hazeeqazfar01/Roboter_Design_Challenge/Pictures/1.jpeg

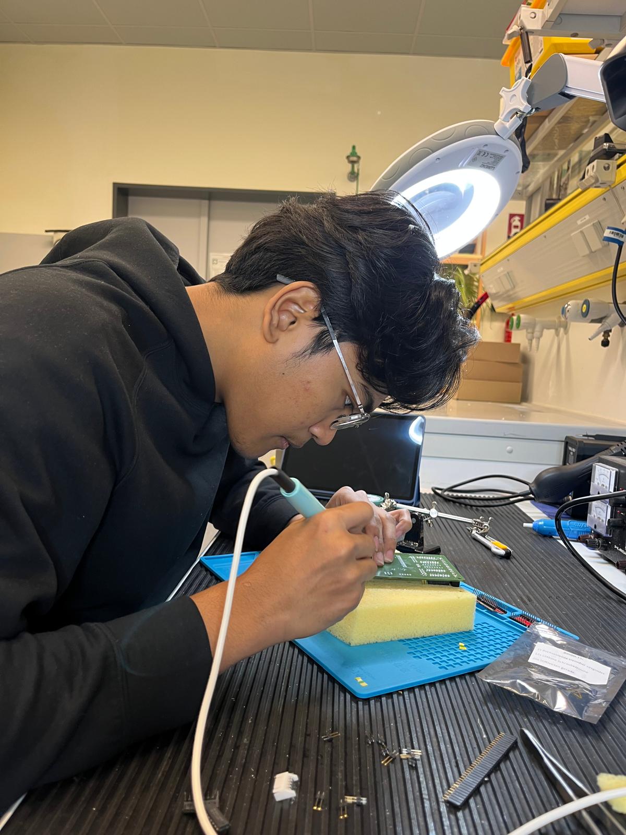
Pictures/1.jpeg
