hazeeqazfar01/Roboter_Design_Challenge/Pictures/2WhatsApp Image 2026-04-02 at 15.36.26.jpeg

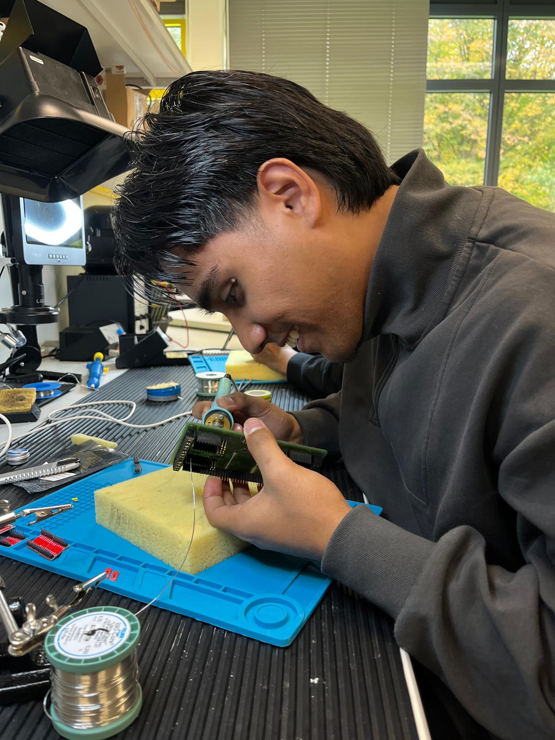
Pictures/2WhatsApp Image 2026-04-02 at 15.36.26.jpeg
