hazeeqazfar01/Roboter_Design_Challenge/Pictures/3.jpeg

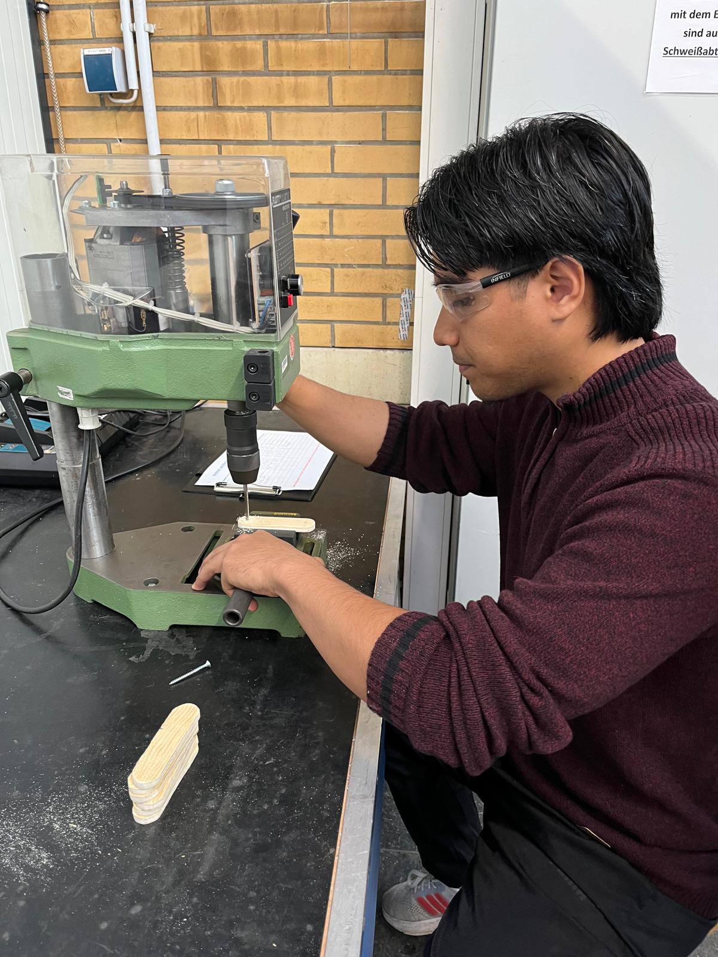
Pictures/3.jpeg
