hazeeqazfar01/Roboter_Design_Challenge/Pictures/4.jpeg

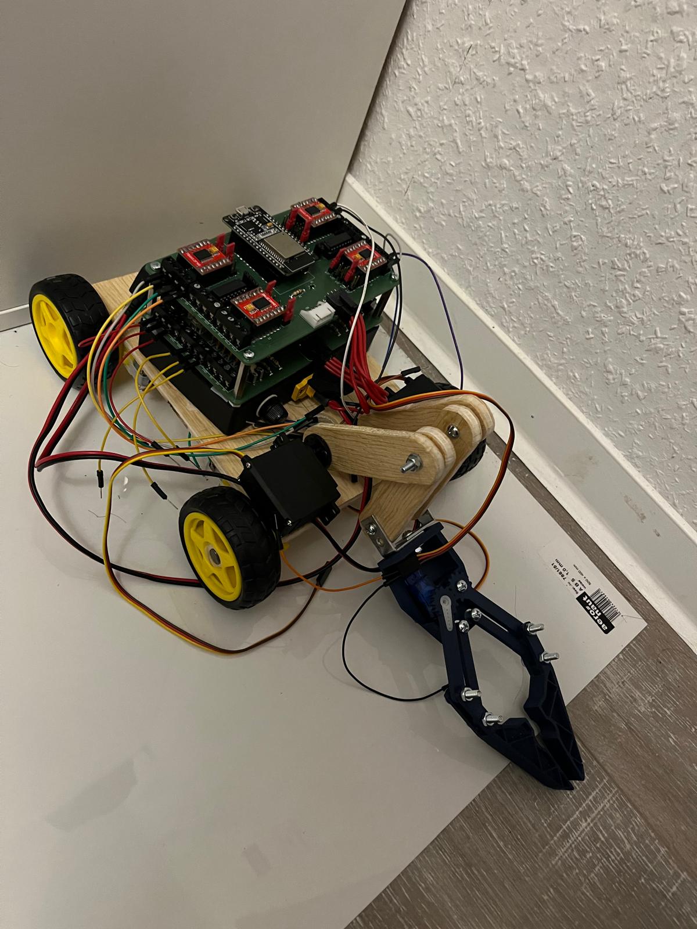
Pictures/4.jpeg
