hazeeqazfar01/Roboter_Design_Challenge/Pictures/5.jpeg

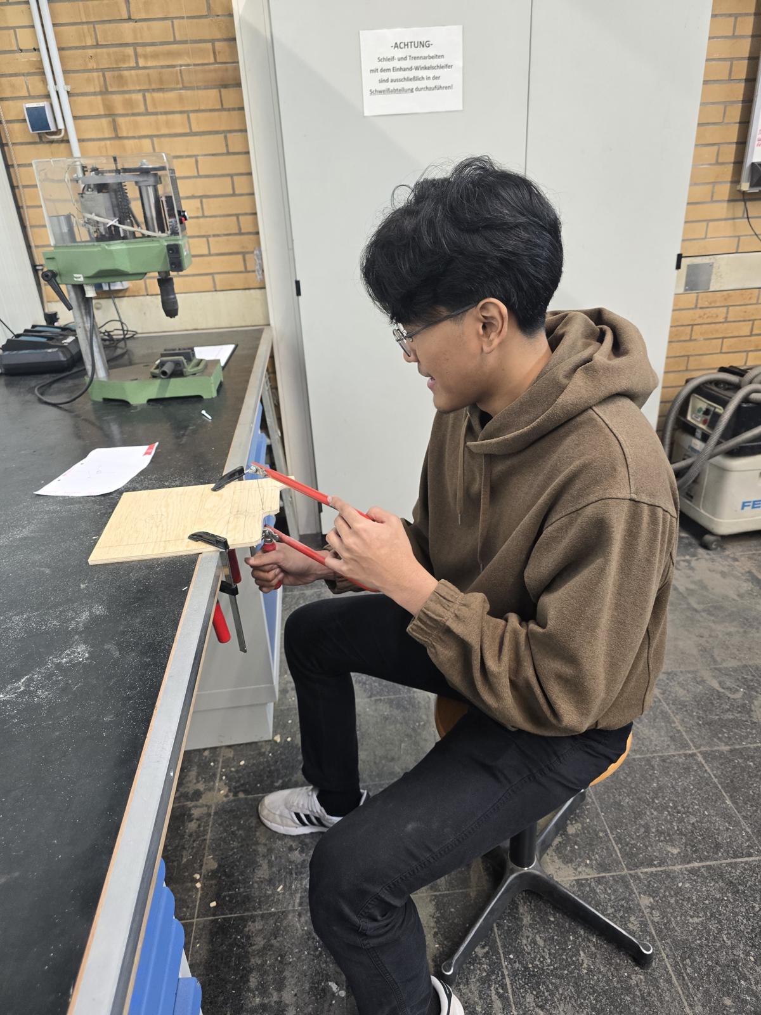
Pictures/5.jpeg
