hazeeqazfar01/Roboter_Design_Challenge/Pictures/7.jpeg

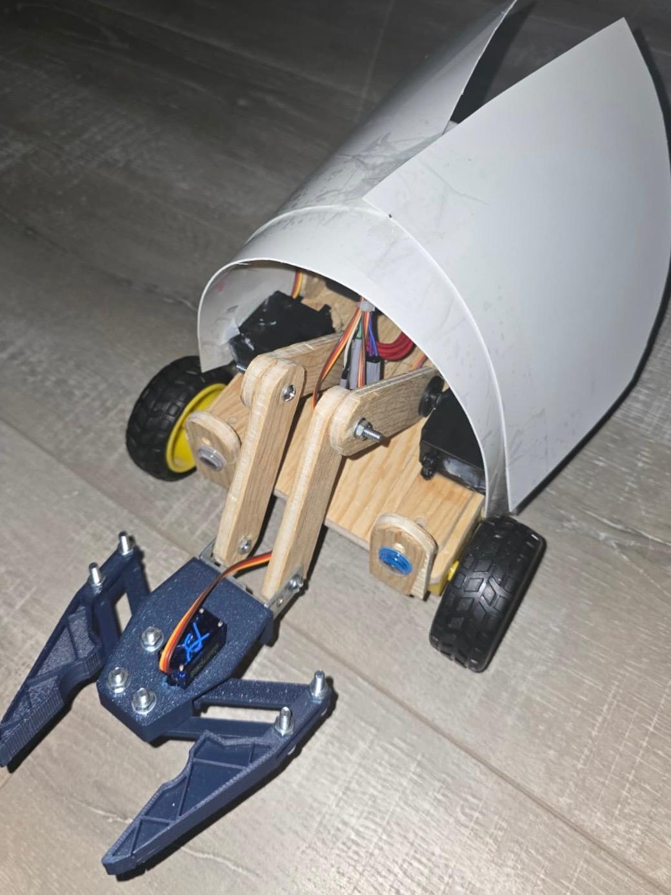
Pictures/7.jpeg
