hazeeqazfar01/Roboter_Design_Challenge/Pictures/8.jpeg

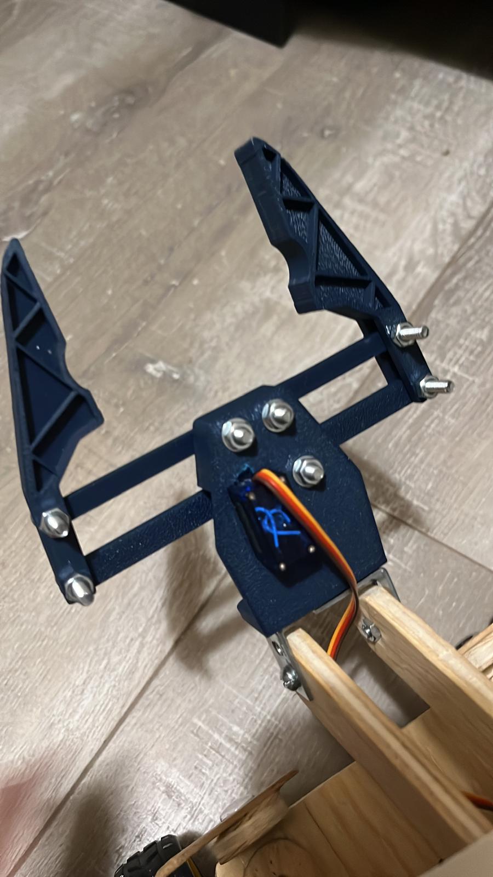
Pictures/8.jpeg
