hazeeqazfar01/Roboter_Design_Challenge/Pictures/9.jpeg

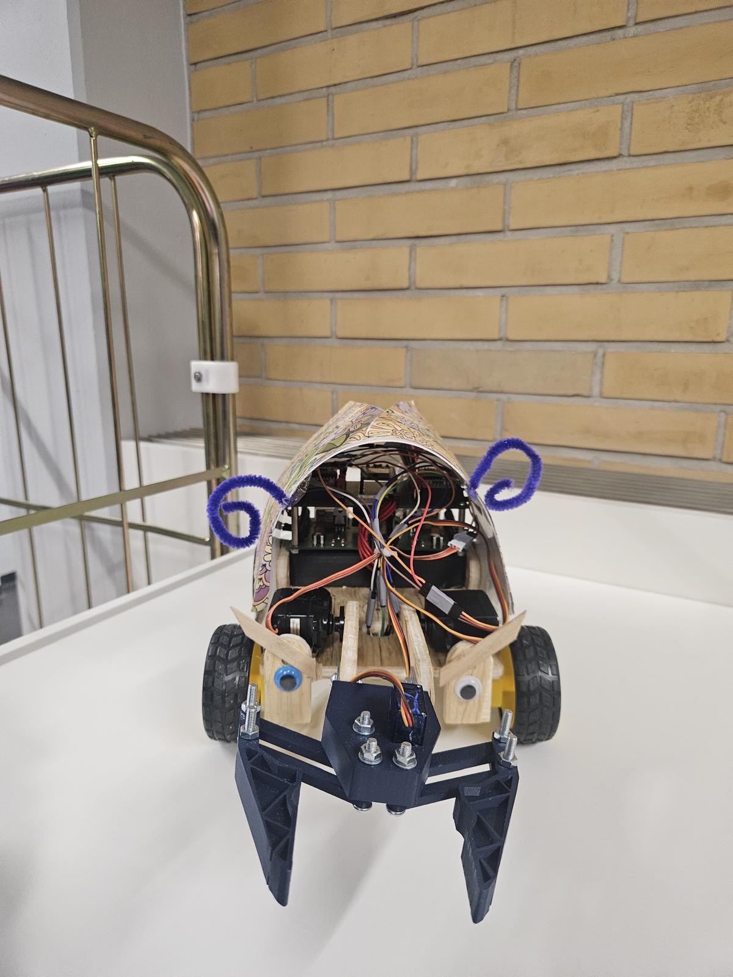
Pictures/9.jpeg
