hazeeqazfar01/Roboter_Design_Challenge/Pictures/45.jpeg

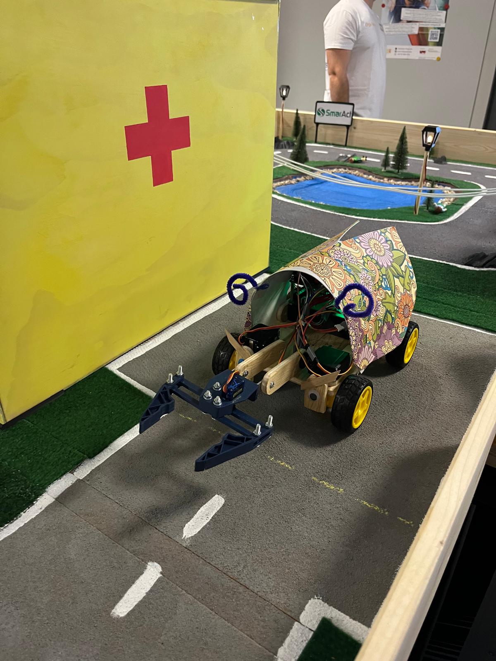
Pictures/45.jpeg
