hazeeqazfar01/Roboter_Design_Challenge/Pictures/334.jpeg

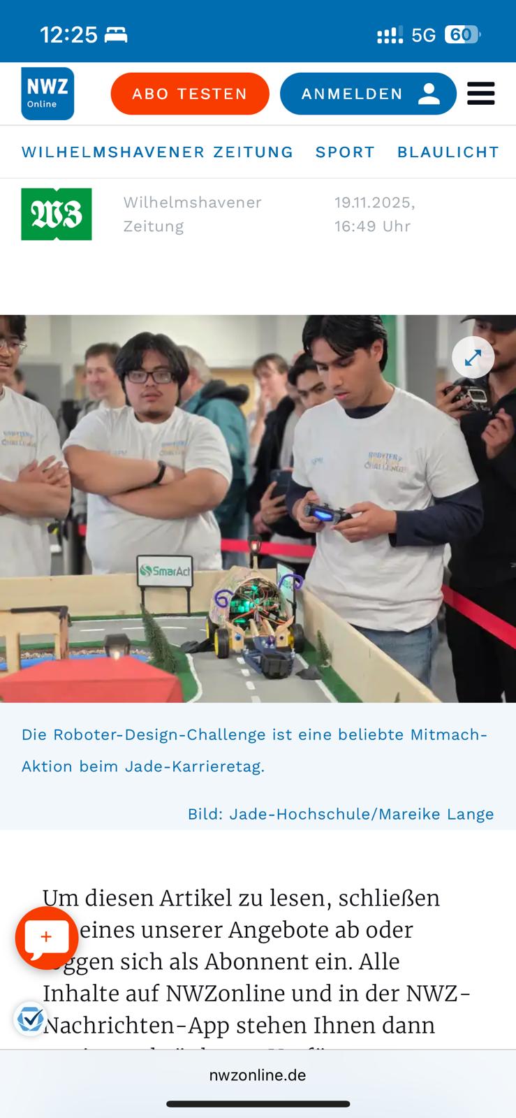
Pictures/334.jpeg
