hazeeqazfar01/Roboter_Design_Challenge/Pictures/3428.jpeg

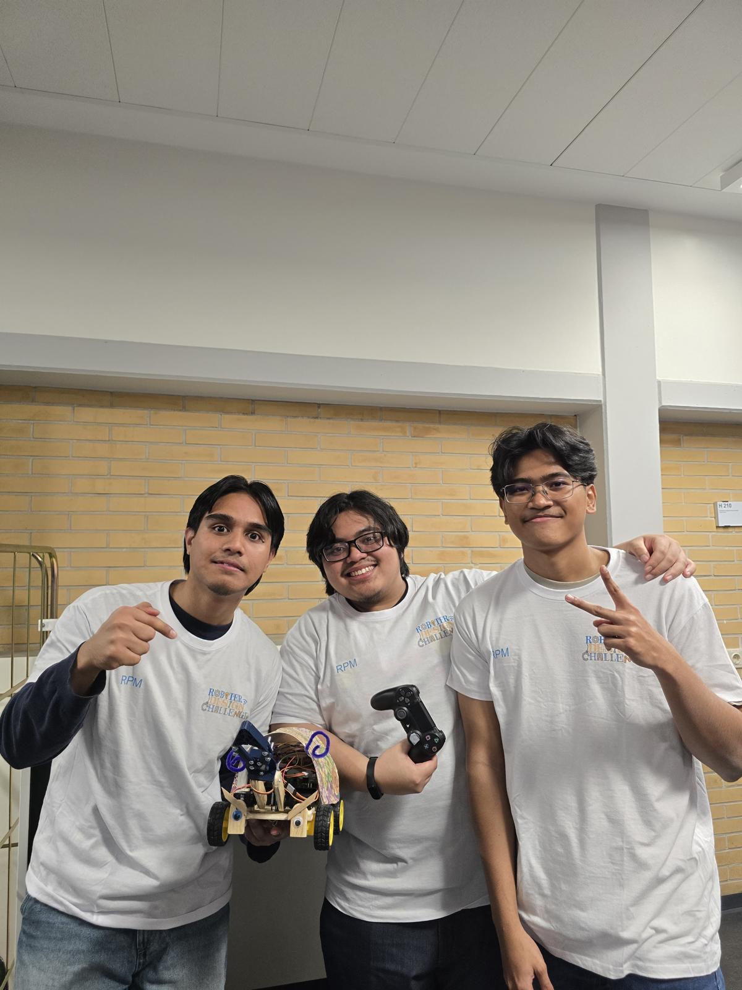
Pictures/3428.jpeg
