hazeeqazfar01/Roboter_Design_Challenge/Pictures/WhatsApp Image 2025-11-19 at 3.07.54 PM.jpeg

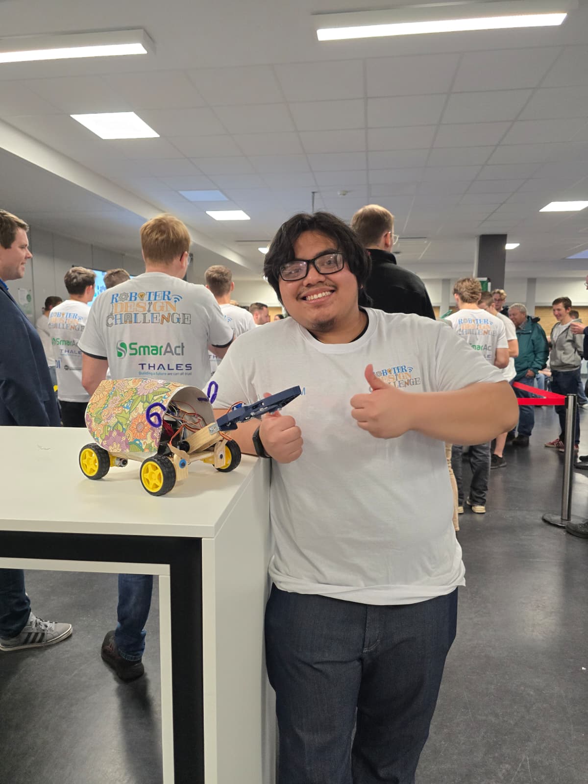
Pictures/WhatsApp Image 2025-11-19 at 3.07.54 PM.jpeg
