hazeeqazfar01/Roboter_Design_Challenge/Pictures/WhatsApp Image 2026-03-29 at 21.02.25.jpeg

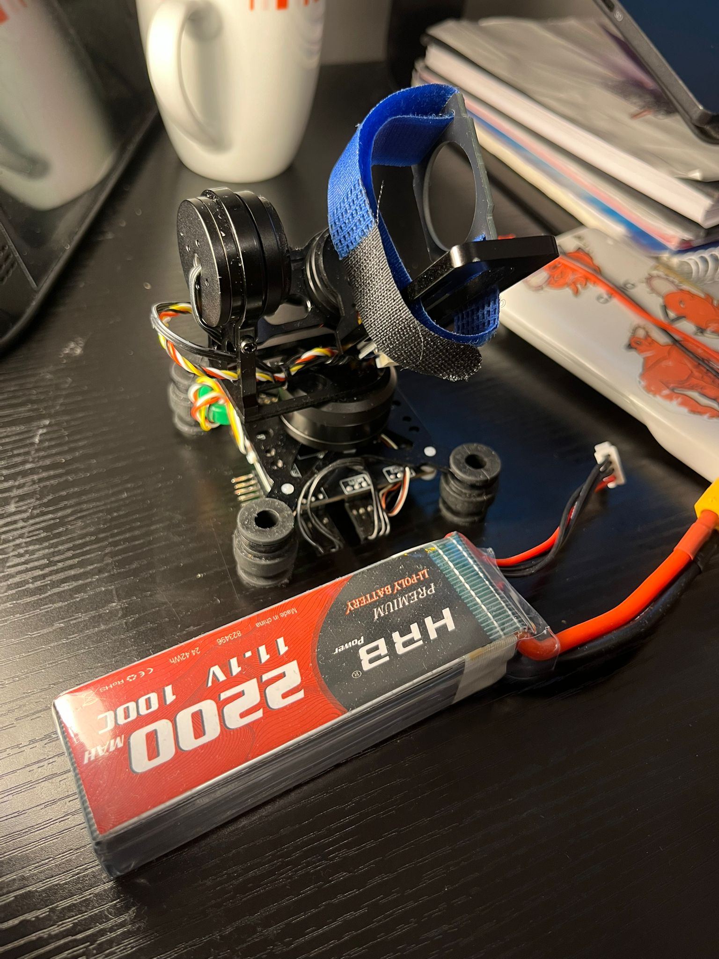
Pictures/WhatsApp Image 2026-03-29 at 21.02.25.jpeg
