hazeeqazfar01/Roboter_Design_Challenge/Documentation_RDC/How to get started/Platine/Steuerplatine.png

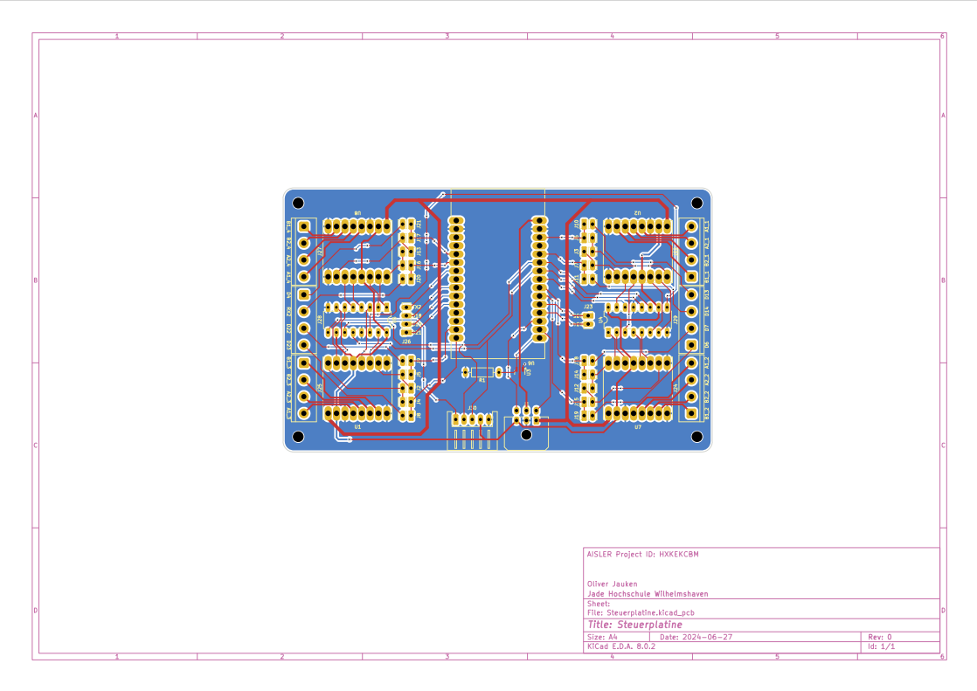
Documentation_RDC/How to get started/Platine/Steuerplatine.png
