hazeeqazfar01/Roboter_Design_Challenge/Documentation_RDC/How to get started/Platine/Steuerplatine_rev1.png

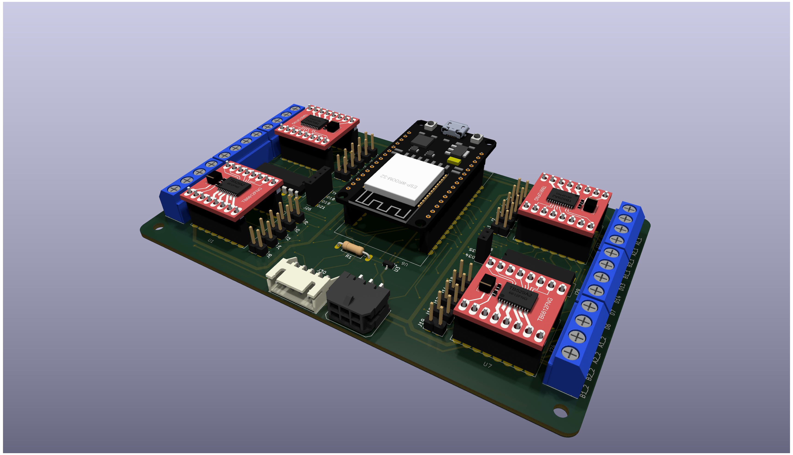
Documentation_RDC/How to get started/Platine/Steuerplatine_rev1.png
