hazeeqazfar01/Roboter_Design_Challenge/Documentation_RDC/How to get started/Platine/versorgungsplatine_rev1.jpg

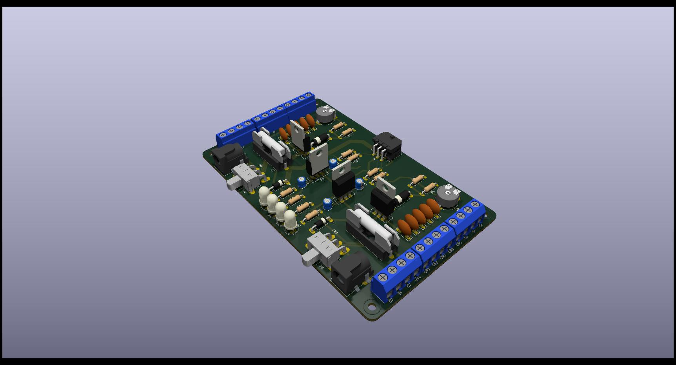
Documentation_RDC/How to get started/Platine/versorgungsplatine_rev1.jpg
